dherrendoerfer/uCNC_controller/Extras/Rod-Robin/Z-Axis-Tool/Rod-Robin-Z-Tool_A.stl

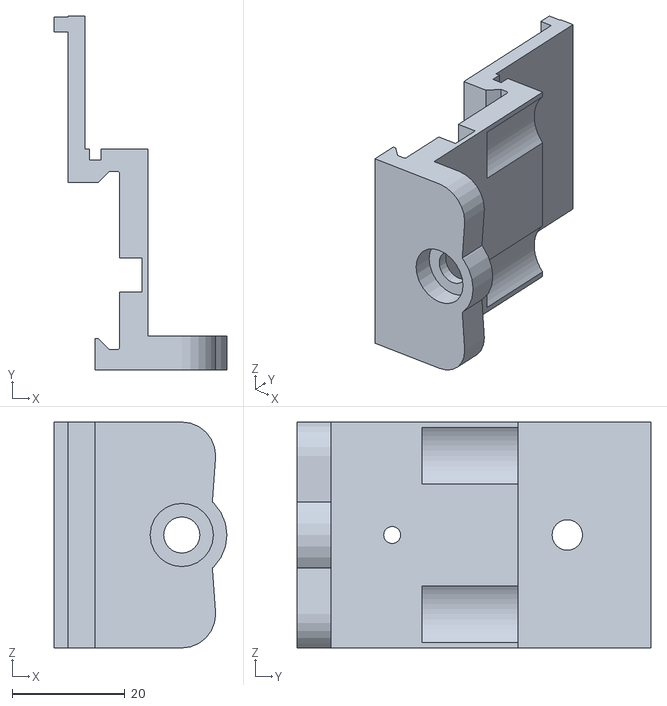
[picture p15: CAD file, 2017-02-15]
Extras/Rod-Robin/Z-Axis-Tool/Rod-Robin-Z-Tool_A.stl
30.6 x 62.6 x 40.0
