dherrendoerfer/uCNC_controller/Extras/Plotter_v4/Plotter_v4_Pillar_2.stl

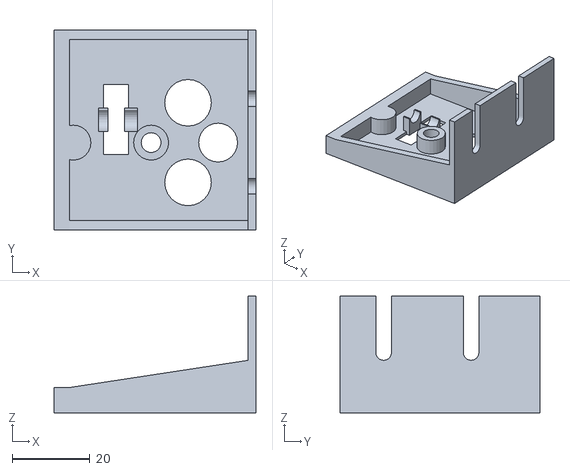
[picture p16: CAD file, 2018-01-10]
Extras/Plotter_v4/Plotter_v4_Pillar_2.stl
52.0 x 51.5 x 30.0
