dherrendoerfer/uCNC_controller/Extras/Rod-Robin/Rod-Robin-Pillar-B.stl

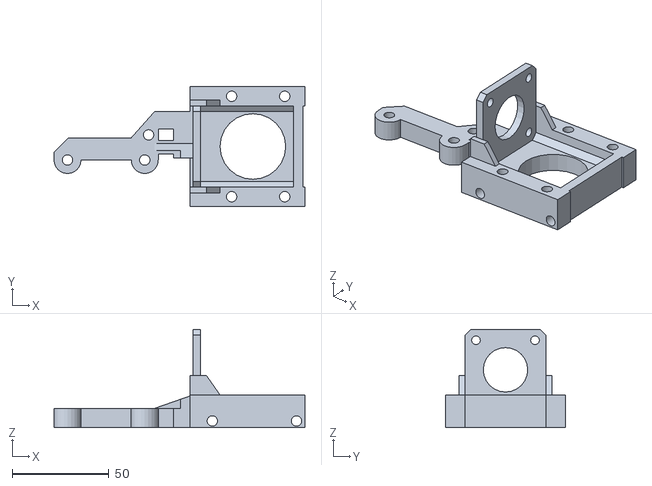
[picture p17: CAD file, 2017-02-15]
Extras/Rod-Robin/Rod-Robin-Pillar-B.stl
130.0 x 62.0 x 51.0
