dherrendoerfer/uCNC_controller/Extras/Rod-Robin/Z-Axis-Tool/Rod-Robin-Z-Tool_E.stl

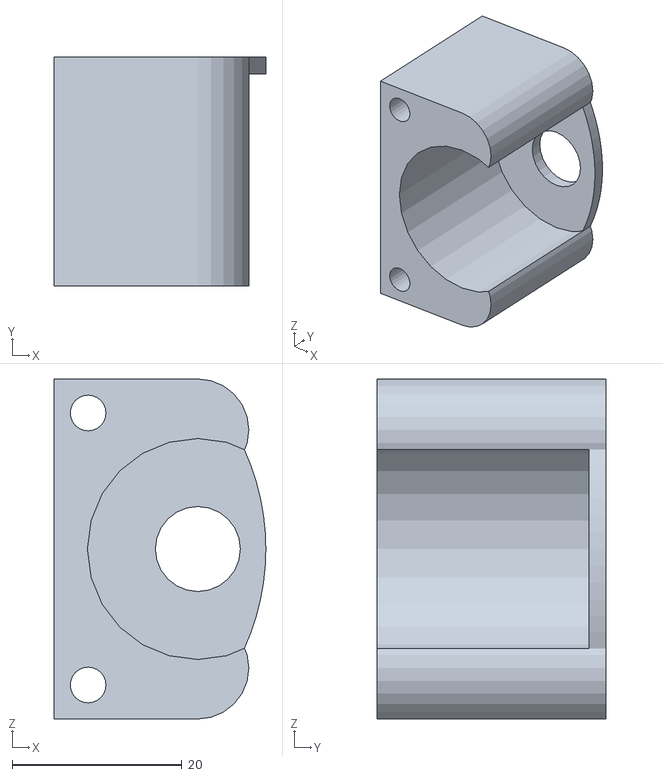
[picture p18: CAD file, 2017-02-15]
Extras/Rod-Robin/Z-Axis-Tool/Rod-Robin-Z-Tool_E.stl
24.9 x 27.0 x 40.0
