dherrendoerfer/uCNC_controller/Extras/Plotter_v4/Plotter_v4_Tool_Sled.stl

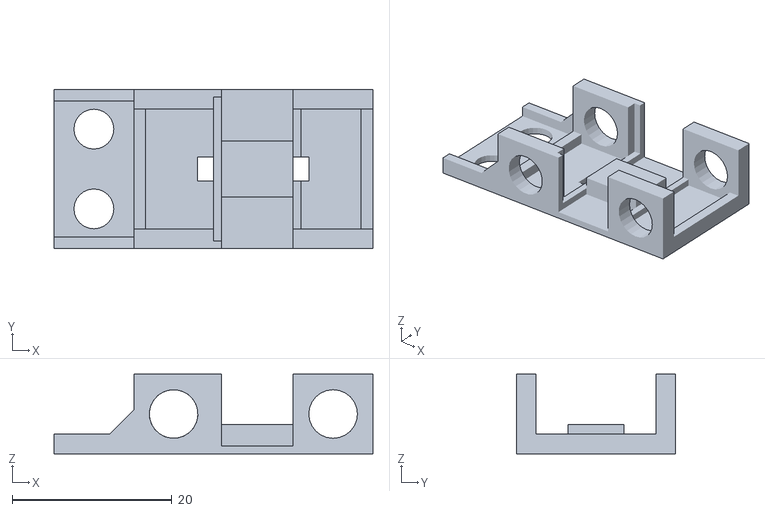
[picture p19: CAD file, 2018-01-10]
Extras/Plotter_v4/Plotter_v4_Tool_Sled.stl
40.0 x 20.0 x 10.0
