dherrendoerfer/uCNC_controller/Extras/Rod-Robin/Rod-Robin-H-Base-A.stl

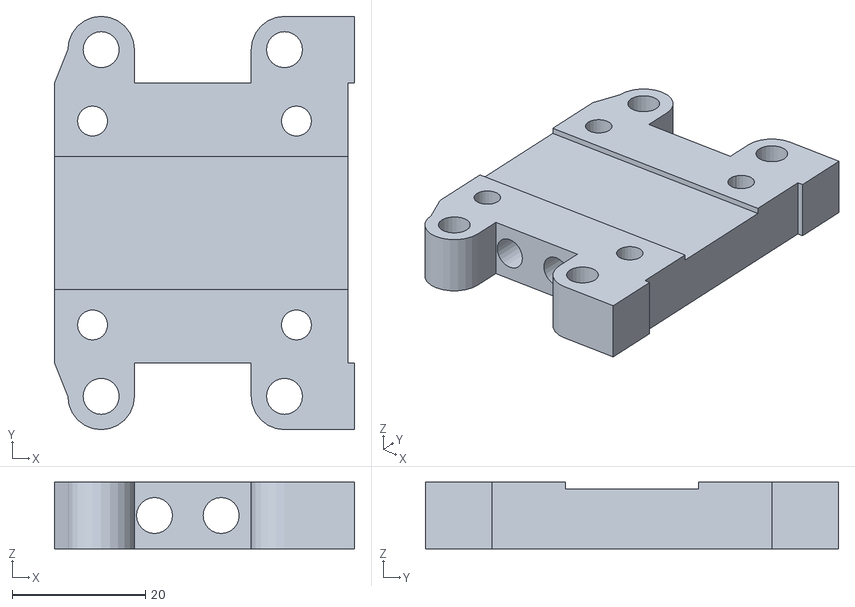
[picture p20: CAD file, 2017-02-15]
Extras/Rod-Robin/Rod-Robin-H-Base-A.stl
45.0 x 62.0 x 10.0
