dherrendoerfer/uCNC_controller/Extras/Rod-Robin/Z-Axis-Tool/Rod-Robin-Z-Tool_D.stl

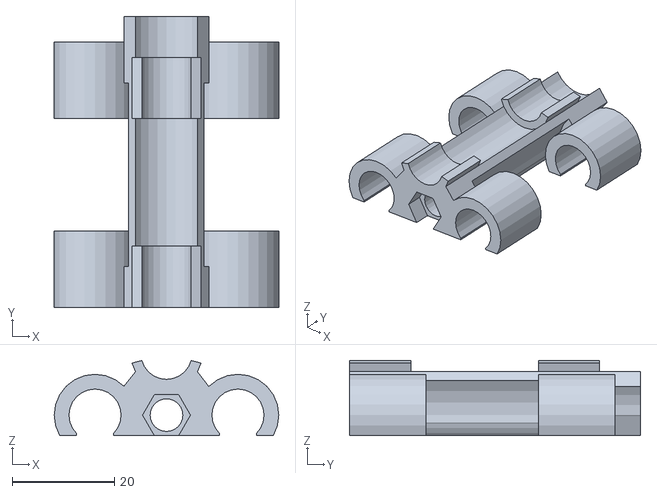
[picture p21: CAD file, 2017-02-15]
Extras/Rod-Robin/Z-Axis-Tool/Rod-Robin-Z-Tool_D.stl
44.0 x 57.0 x 14.7
