dherrendoerfer/uCNC_controller/Extras/Plotter_v4/Plotter_v4_AllParts.stl

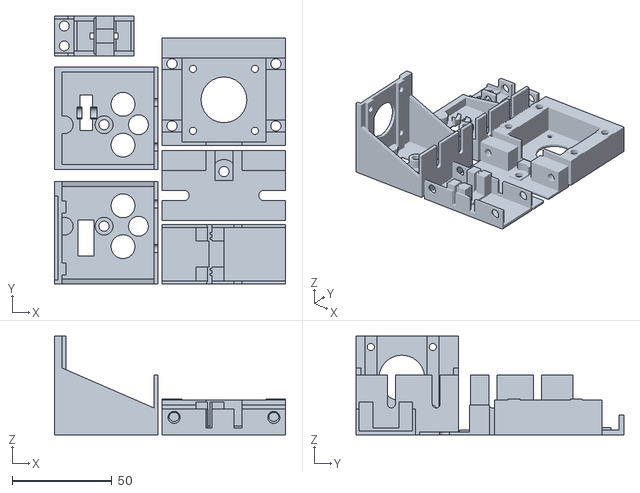
[picture p22: CAD file, 2016-12-31]
Extras/Plotter_v4/Plotter_v4_AllParts.stl
116.1 x 134.5 x 49.5
