dherrendoerfer/uCNC_controller/Extras/Rod-Robin/Rod-Robin-H-Base-C.stl

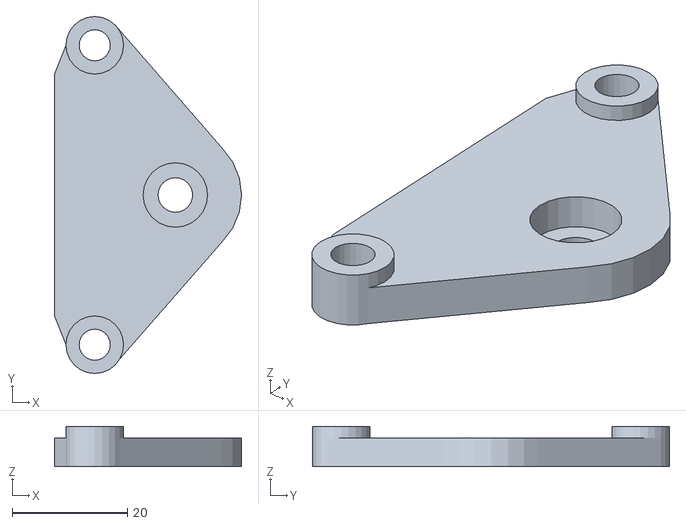
[picture p23: CAD file, 2017-02-15]
Extras/Rod-Robin/Rod-Robin-H-Base-C.stl
32.5 x 62.0 x 7.00
