dherrendoerfer/uCNC_controller/Extras/Rod-Robin/Rod-Robin-H-Base-B.stl

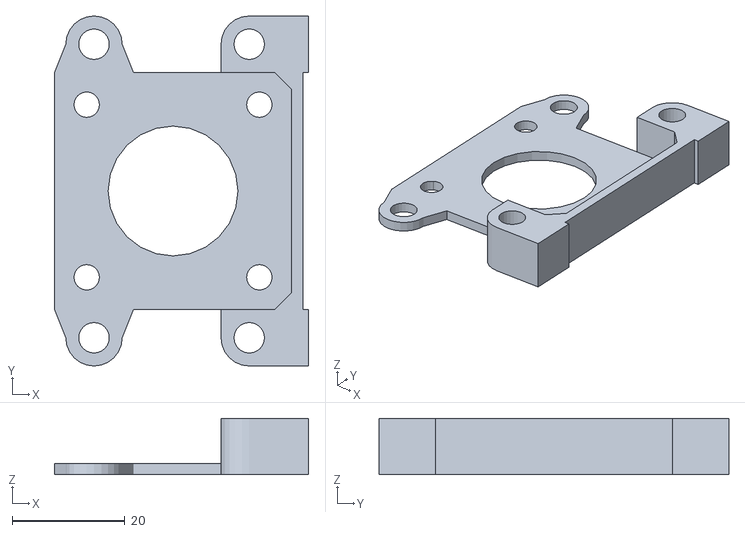
[picture p24: CAD file, 2017-02-15]
Extras/Rod-Robin/Rod-Robin-H-Base-B.stl
45.0 x 62.0 x 10.0
