dherrendoerfer/uCNC_controller/Extras/Rod-Robin/Rod-Robin-Table-A.stl

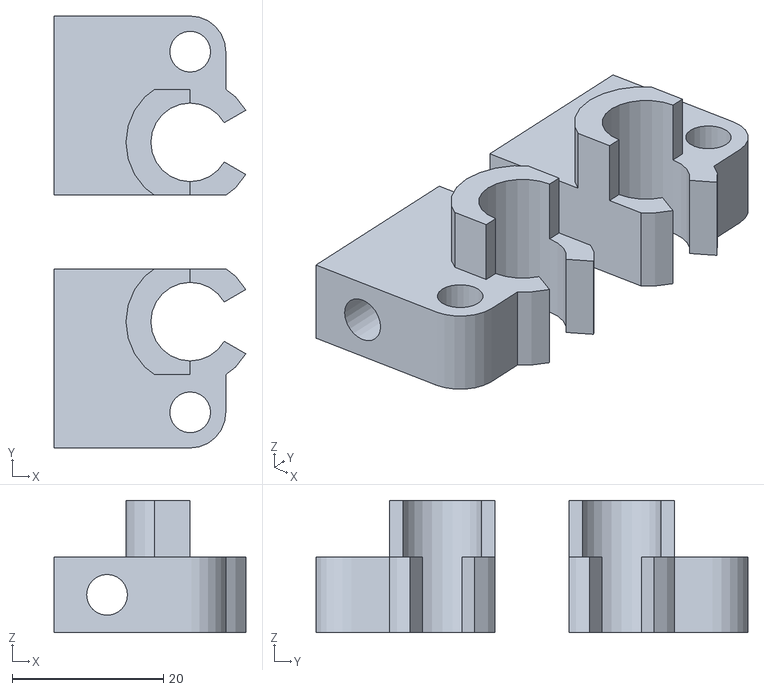
[picture p25: CAD file, 2017-02-15]
Extras/Rod-Robin/Rod-Robin-Table-A.stl
25.4 x 57.2 x 17.5
