dherrendoerfer/uCNC_controller/beta/uCNC_controller_v6/uCNC_move_planner.ino

/*
 * This file is part of uCNC_controller.
 *
 * Copyright (C) 2016,2017  D.Herrendoerfer
 *
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
 *   You should have received a copy of the GNU General Public License
 *   along with uCNC_controller.  If not, see <http://www.gnu.org/licenses/>.
 */

#define PLAN_MAX 7

struct planItem {
  unsigned int lineNo;
  posval_t targetX, targetY, targetZ;
  unsigned int feedHz;
  unsigned int feedStartHz;
} movePlan[8];

int currentPlanItem = 0;
int nextPlanItem = 0;

void plan_line(posval_t x2, posval_t y2, posval_t z2, float feedrate)
{
  posval_t n, deltax, deltay, deltaz, sgndeltax, sgndeltay, sgndeltaz, deltaxabs, deltayabs, deltazabs, x, y, z, maxdeltaabs;
  unsigned int feedHz; 
  unsigned int startHz; 

  deltax = x2 - X;
  deltay = y2 - Y;
  deltaz = z2 - Z;
  deltaxabs = abs(deltax);
  deltayabs = abs(deltay);
  deltazabs = abs(deltaz);
  sgndeltax = sgn(deltax);
  sgndeltay = sgn(deltay);
  sgndeltaz = sgn(deltaz);
  x = deltaxabs >> 1;
  y = deltayabs >> 1;
  z = deltazabs >> 1;

  // dX is biggest
  if(deltaxabs >= deltayabs && deltaxabs >= deltazabs){
    maxdeltaabs = deltaxabs;
    feedHz = feedrate * stepNumPerMillimeter_X;
    startHz = stepIssueStartFreq_X;
    
    if (stepIssueFrequency_X < feedHz)
      feedHz = stepIssueFrequency_X;    
  }
  // dY is biggest
  else if(deltayabs >= deltaxabs && deltayabs >= deltazabs){
    maxdeltaabs = deltayabs;
    feedHz = feedrate * stepNumPerMillimeter_Y;
    startHz = stepIssueStartFreq_Y;
    
    if (stepIssueFrequency_Y < feedHz)
      feedHz = stepIssueFrequency_Y;
  }
  // dZ is biggest
  else if(deltazabs >= deltaxabs && deltazabs >= deltayabs){
    maxdeltaabs = deltazabs;
    feedHz = feedrate * stepNumPerMillimeter_Z;
    startHz = stepIssueStartFreq_Z;

    if (stepIssueFrequency_Z < feedHz)
      feedHz = stepIssueFrequency_Z;
  }
  Serial.print("Feed rate:");
  Serial.print(feedHz);
  Serial.println("Hz");
  
  if (deltaxabs)  
    mStepperX.plan(0, sgndeltax, maxdeltaabs, deltaxabs, x, feedHz, startHz);

  if (deltayabs)  
    mStepperY.plan(0, sgndeltay, maxdeltaabs, deltayabs, y, feedHz, startHz);

  if (deltazabs)  
    mStepperZ.plan(0, sgndeltaz, maxdeltaabs, deltazabs, z, feedHz, startHz);

  X = x2;
  Y = y2;
  Z = z2;
}

void addPlanItem(unsigned int lineNo, posval_t x, posval_t y, posval_t z, unsigned int feedrateHz)
{
  movePlan[currentPlanItem].lineNo = lineNo;
  movePlan[currentPlanItem].targetX = x;
  movePlan[currentPlanItem].targetY = y;
  movePlan[currentPlanItem].targetZ = z;
  movePlan[currentPlanItem].feedHz = feedrateHz;
  
  if (++currentPlanItem == PLAN_MAX)
    currentPlanItem = 0;
}

void syncPlan()
{

}
