dherrendoerfer/uCNC_controller/uCNC_controller/uCNC_builtin.ino

/*
 * This file is part of uCNC_controller.
 *
 * Copyright (C) 2014  D.Herrendoerfer
 *
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
 *   You should have received a copy of the GNU General Public License
 *   along with uCNC_controller.  If not, see <http://www.gnu.org/licenses/>.
 */

/* Built-in functions for setup and debug purposes 
 * using these may require some tweaking           */

#ifdef BUILTIN
void calibratePattern()
{
  int i=0;

  /*Draw a line pattern in absolute step mode*/
  drawline(50,50,1000,50);
  drawline(1000,150,50,150);
  drawline(50,250,1000,250);
  drawline(1000,350,50,350);

  for (i=50; i<1000; i+=50)
    drawline(i,30,i,70);

  for (i=100; i<1000; i+=100)
    drawline(i,30,i,170);

  for (i=200; i<1000; i+=200)
    drawline(i,30,i,270);

  for (i=400; i<1000; i+=400)
    drawline(i,30,i,370);

  /*Draw a line pattern in 5,10,20,40mm spacing*/
  drawlinePos(5,25,60,25);
  drawlinePos(60,30,5,30);
  drawlinePos(5,35,60,35);
  drawlinePos(60,40,5,40);
  
  for (i=5; i<60; i+=5)
    drawlinePos(i,23,i,27);
  
  for (i=10; i<60; i+=10)
    drawlinePos(i,23,i,32);

  for (i=20; i<60; i+=20)
    drawlinePos(i,23,i,37);

  for (i=40; i<60; i+=40)
    drawlinePos(i,23,i,42);
}
#endif

#ifdef BUILTIN
void dumpSettings()
{
  Serial.print("Hello, this is uCNC_contoller version ");
  Serial.println(uCNC_Version,1);
  Serial.println("");
  Serial.println("current settings are:");
  Serial.println("");
  Serial.print("motorMode:");
  Serial.println(motorMode);
  Serial.println("Stepper positions:");
  Serial.print("X:");
  Serial.println(X);
  Serial.print("Y:");
  Serial.println(Y);
  Serial.print("Z:");
  Serial.println(Z);
  Serial.println("Absolute positions:");
  Serial.print("posX:");
  Serial.println(posX,3);
  Serial.print("posY:");
  Serial.println(posY,3);
  Serial.print("posZ:");
  Serial.println(posZ,3);
  Serial.println("Stepper settings:");
  Serial.print("stepsPerMillimeter_X:");
  Serial.println(stepsPerMillimeter_X, 3);
  Serial.print("stepsPerMillimeter_Y:");
  Serial.println(stepsPerMillimeter_Y, 3);
  Serial.print("stepsPerMillimeter_Z:");
  Serial.println(stepsPerMillimeter_Z, 3);
  Serial.println("Servo settings:");
  Serial.print("servoPosZfactor:");
  Serial.println(servoPosZfactor, 3);
  Serial.print("servoPosMax:");
  Serial.println(servoPosMax);
  Serial.print("servoPosMin:");
  Serial.println(servoPosMin);
  Serial.print("servoToolInc:");
  Serial.println(servoToolInc);
  Serial.print("EOM."); 
}
#endif
