dherrendoerfer/uCNC_controller/Extras/LED-HMD/led-hmd/led-hmd.ino

/*
 * This file is part of uCNC_controller.
 *
 * Copyright (C) 2017  D.Herrendoerfer
 *
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
 *   You should have received a copy of the GNU General Public License
 *   along with uCNC_controller.  If not, see <http://www.gnu.org/licenses/>.
 */

#include "FastLED.h"
 
#define DATA_PIN    6
#define LED_TYPE    WS2812B
#define COLOR_ORDER GRB
#define NUM_LEDS    506
#define BRIGHTNESS  25
 
CRGB leds[NUM_LEDS];

/* pix/Stormtrooper Pixel Head.png */
const PROGMEM unsigned char image0[]={231, 233, 232, 231, 233, 232, 231, 233, 232, 231, 233, 232, 231, 233, 232, 231, 233, 232, 231, 233, 232, 231, 233, 232, 231, 233, 232, 231, 233, 232, 231, 233, 232, 231, 233, 232, 231, 233, 232, 231, 233, 232, 231, 233, 232, 231, 233, 232, 231, 233, 232, 231, 233, 232, 231, 233, 232, 231, 233, 232, 231, 233, 232, 206, 210, 209, 206, 210, 209, 206, 210, 209, 206, 210, 209, 231, 233, 232, 231, 233, 232, 231, 233, 232, 231, 233, 232, 231, 233, 232, 231, 233, 232, 231, 233, 232, 231, 233, 232, 231, 233, 232, 206, 210, 209, 206, 210, 209, 206, 210, 209, 206, 210, 209, 206, 210, 209, 206, 210, 209, 206, 210, 209, 206, 210, 209, 231, 233, 232, 231, 233, 232, 231, 233, 232, 231, 233, 232, 231, 233, 232, 231, 233, 232, 231, 233, 232, 231, 233, 232, 206, 210, 209, 206, 210, 209, 206, 210, 209, 206, 210, 209, 206, 210, 209, 206, 210, 209, 206, 210, 209, 206, 210, 209, 206, 210, 209, 206, 210, 209, 231, 233, 232, 231, 233, 232, 231, 233, 232, 231, 233, 232, 0, 0, 0, 231, 233, 232, 231, 233, 232, 231, 233, 232, 231, 233, 232, 206, 210, 209, 206, 210, 209, 206, 210, 209, 206, 210, 209, 206, 210, 209, 206, 210, 209, 206, 210, 209, 206, 210, 209, 206, 210, 209, 206, 210, 209, 231, 233, 232, 231, 233, 232, 231, 233, 232, 231, 233, 232, 0, 0, 0, 0, 0, 0, 0, 0, 0, 231, 233, 232, 231, 233, 232, 231, 233, 232, 231, 233, 232, 206, 210, 209, 206, 210, 209, 206, 210, 209, 206, 210, 209, 206, 210, 209, 206, 210, 209, 206, 210, 209, 206, 210, 209, 206, 210, 209, 2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
0, 209, 206, 210, 209, 0, 0, 0, 0, 0, 0, 206, 210, 209, 206, 210, 209, 156, 158, 157, 0, 0, 0, 156, 158, 157, 156, 158, 157, 25, 25, 25, 46, 48, 47, 46, 48, 47, 25, 25, 25, 154, 156, 155, 154, 156, 155, 0, 0, 0, 154, 156, 155, 206, 210, 209, 206, 210, 209, 0, 0, 0, 206, 210, 209, 206, 210, 209, 0, 0, 0, 255, 255, 255, 0, 0, 0, 156, 158, 157, 46, 48, 47, 25, 25, 25, 25, 25, 25, 46, 48, 47, 154, 156, 155, 0, 0, 0, 255, 255, 255, 0, 0, 0, 206, 210, 209, 206, 210, 209, 206, 210, 209, 156, 158, 157, 0, 0, 0, 255, 255, 255, 46, 48, 47, 46, 48, 47, 25, 25, 25, 25, 25, 25, 46, 48, 47, 46, 48, 47, 154, 156, 155, 0, 0, 0, 154, 156, 155, 206, 210, 209, 206, 210, 209, 206, 210, 209, 206, 210, 209, 0, 0, 0, 0, 0, 0, 0, 0, 0, 0, 0, 0, 206, 210, 209, 206, 210, 209, 206, 210, 209, 0, 0, 0, 0, 0, 0, 0, 0, 0, 0, 0, 0, 0, 0, 0, 0, 0, 0, };

/* flaming eye */
const PROGMEM unsigned char image1[]={0, 0, 0, 0, 0, 0, 0, 0, 0, 0, 0, 0, 0, 0, 0, 0, 0, 0, 0, 0, 0, 0, 0, 0, 0, 0, 0, 0, 0, 0, 0, 0, 0, 0, 0, 0, 0, 0, 0, 0, 0, 0, 0, 0, 0, 0, 0, 0, 0, 0, 0, 0, 0, 0, 0, 0, 0, 0, 0, 0, 0, 0, 0, 0, 0, 0, 0, 0, 0, 0, 0, 0, 0, 0, 0, 0, 0, 0, 0, 0, 0, 0, 0, 0, 0, 0, 0, 0, 0, 0, 0, 0, 0, 0, 0, 0, 0, 0, 0, 0, 0, 0, 0, 0, 0, 0, 0, 0, 0, 0, 0, 0, 0, 0, 0, 0, 0, 0, 0, 0, 0, 0, 0, 0, 0, 0, 0, 0, 0, 0, 0, 0, 0, 0, 0, 0, 0, 0, 0, 0, 0, 0, 0, 0, 0, 0, 0, 0, 0, 0, 0, 0, 0, 0, 0, 0, 0, 0, 0, 0, 0, 0, 0, 0, 0, 0, 0, 0, 0, 0, 0, 0, 0, 0, 0, 0, 0, 0, 0, 0, 0, 0, 0, 0, 0, 0, 0, 0, 0, 255, 17, 0, 0, 0, 0, 0, 0, 0, 0, 0, 0, 0, 0, 0, 0, 0, 0, 0, 0, 0, 0, 0, 0, 0, 0, 0, 0, 0, 0, 0, 0, 0, 0, 0, 0, 0, 0, 0, 0, 0, 0, 0, 0, 0, 0, 0, 0, 255, 17, 0, 0, 0, 0, 0, 0, 0, 0, 0, 0, 0, 0, 0, 0, 0, 0, 0, 0, 0, 0, 0, 0, 0, 0, 0, 0, 0, 0, 0, 0, 0, 0, 0, 0, 0, 0, 0, 0, 0, 0, 0, 0, 0, 0, 0, 0, 0, 0, 0, 0, 0, 0, 0, 0, 0, 0, 0, 0, 0, 0, 0, 0, 0, 0, 0, 0, 0, 0, 0, 0, 0, 0, 0, 255, 17, 0, 0, 0, 0, 0, 0, 0, 0, 0, 0, 0, 0, 0, 0, 0, 0, 0, 0, 0, 0, 0, 0, 0, 0, 0, 0, 0, 0, 0, 0, 0, 0, 0, 0, 0, 0, 0, 0, 0, 0, 0, 0, 0, 0, 0, 0, 0, 0, 0, 0, 0, 0, 0, 0, 0, 219, 15, 0, 219, 15, 0, 0, 0, 0, 0, 0, 0, 0, 0, 0, 0, 0, 0, 0, 0, 0, 0, 0, 0, 0, 0, 0, 0, 0, 0, 0, 0, 0, 0, 0, 0, 255, 255, 255, 255, 255, 255, 255, 255, 255, 255, 255, 255, 255, 255, 255, 255, 255, 255, 255, 255, 255, 255, 255, 255, 0, 0, 0, 0, 0, 0, 219, 15, 0, 219, 15, 0, 0, 0, 0, 0, 0, 0, 0, 0, 0, 255, 17, 0, 0, 0, 0, 0, 0, 0, 0, 0, 0, 0, 0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

/* pix/smiley-1635449_960_720.png */
const PROGMEM unsigned char image2[]={0, 0, 0, 0, 0, 0, 0, 0, 0, 0, 0, 0, 0, 0, 0, 0, 0, 0, 0, 0, 0, 0, 0, 0, 25, 25, 0, 58, 57, 0, 79, 76, 0, 79, 76, 0, 58, 57, 0, 25, 25, 0, 0, 0, 0, 0, 0, 0, 0, 0, 0, 9, 8, 0, 0, 0, 0, 0, 0, 0, 0, 0, 0, 0, 0, 0, 255, 255, 0, 255, 255, 0, 0, 0, 0, 0, 0, 0, 0, 0, 0, 0, 0, 0, 9, 8, 0, 0, 0, 0, 0, 0, 0, 0, 0, 0, 0, 0, 0, 255, 255, 0, 255, 251, 0, 255, 244, 0, 254, 240, 0, 252, 239, 0, 252, 239, 0, 254, 240, 0, 255, 244, 0, 255, 251, 0, 255, 255, 0, 0, 0, 0, 0, 0, 0, 0, 0, 0, 0, 0, 0, 0, 0, 0, 0, 0, 0, 255, 248, 0, 255, 245, 0, 255, 252, 0, 254, 241, 0, 255, 241, 0, 255, 242, 0, 255, 242, 0, 255, 241, 0, 254, 241, 0, 255, 252, 0, 255, 245, 0, 255, 248, 0, 0, 0, 0, 0, 0, 0, 0, 0, 0, 0, 0, 0, 0, 0, 0, 255, 255, 0, 251, 238, 0, 255, 248, 0, 0, 0, 0, 0, 0, 0, 255, 245, 0, 254, 244, 0, 254, 241, 0, 254, 242, 0, 254, 243, 0, 255, 246, 0, 0, 0, 0, 0, 0, 0, 255, 248, 0, 251, 238, 0, 255, 255, 0, 0, 0, 0, 0, 0, 0, 0, 0, 0, 0, 0, 0, 0, 0, 0, 249, 238, 0, 253, 248, 0, 0, 0, 0, 16, 15, 0, 0, 0, 0, 0, 0, 0, 255, 252, 0, 253, 240, 0, 253, 239, 0, 255, 252, 0, 0, 0, 0, 0, 0, 0, 14, 14, 0, 0, 0, 0, 253, 249, 0, 248, 238, 0, 0, 0, 0, 0, 0, 0, 0, 0, 0, 0, 0, 0, 0, 0, 0, 254, 250, 0, 249, 236, 0, 255, 255, 0, 0, 0, 0, 0, 0, 0, 5, 5, 0, 0, 0, 0, 0, 0, 0, 255, 249, 0, 255, 248, 0, 215, 204, 0, 0, 0, 0, 5, 5, 0, 0, 0, 0, 0, 0, 0, 255, 255, 0, 249, 236, 0, 254, 250, 0, 0, 0, 0, 0, 0, 0, 0, 0, 0, 0, 0, 0, 255, 255, 0, 251, 237, 0, 255, 243, 0, 252, 240, 0, 0, 0, 0, 1, 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

/* pix/new/smiley-1635449_960_720 Kopie.png */
const PROGMEM unsigned char image3[]={0, 0, 0, 0, 0, 0, 0, 0, 0, 0, 0, 0, 0, 0, 0, 0, 0, 0, 0, 0, 0, 0, 0, 0, 255, 242, 0, 255, 242, 0, 255, 242, 0, 255, 242, 0, 255, 242, 0, 255, 242, 0, 0, 0, 0, 0, 0, 0, 0, 0, 0, 255, 242, 0, 255, 242, 0, 255, 242, 0, 255, 242, 0, 255, 242, 0, 255, 242, 0, 255, 242, 0, 255, 242, 0, 255, 242, 0, 255, 242, 0, 255, 242, 0, 255, 242, 0, 0, 0, 0, 255, 242, 0, 255, 242, 0, 255, 242, 0, 255, 242, 0, 255, 242, 0, 255, 242, 0, 255, 242, 0, 255, 242, 0, 255, 242, 0, 255, 242, 0, 255, 242, 0, 255, 242, 0, 255, 242, 0, 255, 242, 0, 255, 242, 0, 255, 242, 0, 255, 242, 0, 255, 242, 0, 255, 242, 0, 255, 242, 0, 255, 242, 0, 255, 242, 0, 255, 242, 0, 255, 242, 0, 255, 242, 0, 255, 242, 0, 255, 242, 0, 255, 242, 0, 255, 242, 0, 255, 242, 0, 255, 242, 0, 255, 242, 0, 255, 242, 0, 255, 242, 0, 255, 242, 0, 255, 242, 0, 255, 242, 0, 255, 242, 0, 255, 242, 0, 255, 242, 0, 255, 242, 0, 255, 242, 0, 255, 242, 0, 255, 242, 0, 255, 242, 0, 255, 242, 0, 255, 242, 0, 255, 242, 0, 255, 242, 0, 255, 242, 0, 255, 242, 0, 255, 242, 0, 255, 242, 0, 255, 242, 0, 0, 0, 0, 255, 242, 0, 255, 242, 0, 255, 242, 0, 255, 242, 0, 255, 242, 0, 255, 242, 0, 255, 242, 0, 255, 242, 0, 255, 242, 0, 255, 242, 0, 255, 242, 0, 255, 242, 0, 255, 242, 0, 255, 242, 0, 255, 242, 0, 255, 242, 0, 255, 242, 0, 255, 242, 0, 255, 242, 0, 255, 242, 0, 0, 0, 0, 255, 242, 0, 255, 242, 0, 255, 242, 0, 255, 242, 0, 255, 242, 0, 0, 0, 0, 0, 0, 0, 0, 0, 0, 255, 242, 0, 255, 242, 0, 255, 242, 0, 255, 242,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
255, 242, 0, 0, 0, 0, 0, 0, 0, 4, 4, 0, 255, 242, 0, 255, 242, 0, 255, 242, 0, 255, 242, 0, 255, 242, 0, 255, 242, 0, 0, 0, 0, 0, 0, 0, 0, 0, 0, 0, 0, 0, 0, 0, 0, 0, 0, 0, 0, 0, 0, 0, 0, 0, };
/* pix/new/smiley-1635449_960_720.png */
const PROGMEM unsigned char image3b[]={0, 0, 0, 0, 0, 0, 0, 0, 0, 0, 0, 0, 0, 0, 0, 0, 0, 0, 0, 0, 0, 0, 0, 0, 255, 242, 0, 255, 242, 0, 255, 242, 0, 255, 242, 0, 255, 242, 0, 255, 242, 0, 0, 0, 0, 0, 0, 0, 0, 0, 0, 255, 242, 0, 255, 242, 0, 255, 242, 0, 255, 242, 0, 255, 242, 0, 255, 242, 0, 255, 242, 0, 255, 242, 0, 255, 242, 0, 255, 242, 0, 255, 242, 0, 255, 242, 0, 0, 0, 0, 255, 242, 0, 255, 242, 0, 255, 242, 0, 255, 242, 0, 255, 242, 0, 255, 242, 0, 255, 242, 0, 255, 242, 0, 255, 242, 0, 255, 242, 0, 255, 242, 0, 255, 242, 0, 255, 242, 0, 255, 242, 0, 255, 242, 0, 255, 242, 0, 255, 242, 0, 255, 242, 0, 255, 242, 0, 255, 242, 0, 255, 242, 0, 255, 242, 0, 255, 242, 0, 255, 242, 0, 255, 242, 0, 255, 242, 0, 255, 242, 0, 255, 242, 0, 255, 242, 0, 255, 242, 0, 255, 242, 0, 255, 242, 0, 255, 242, 0, 255, 242, 0, 255, 242, 0, 255, 242, 0, 255, 242, 0, 255, 242, 0, 255, 242, 0, 255, 242, 0, 255, 242, 0, 255, 242, 0, 255, 242, 0, 255, 242, 0, 255, 242, 0, 255, 242, 0, 255, 242, 0, 255, 242, 0, 255, 242, 0, 255, 242, 0, 255, 242, 0, 255, 242, 0, 255, 242, 0, 255, 242, 0, 0, 0, 0, 255, 242, 0, 255, 242, 0, 255, 242, 0, 255, 242, 0, 255, 242, 0, 255, 242, 0, 255, 242, 0, 255, 242, 0, 255, 242, 0, 255, 242, 0, 255, 242, 0, 255, 242, 0, 255, 242, 0, 255, 242, 0, 255, 242, 0, 255, 242, 0, 255, 242, 0, 255, 242, 0, 255, 242, 0, 255, 242, 0, 0, 0, 0, 255, 242, 0, 255, 242, 0, 255, 242, 0, 255, 242, 0, 255, 242, 0, 255, 242, 0, 255, 242, 0, 255, 242, 0, 255, 242, 0, 255, 242, 0, 255, 242,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
, 242, 0, 255, 242, 0, 255, 242, 0, 255, 242, 0, 255, 242, 0, 0, 0, 0, 0, 0, 0, 4, 4, 0, 255, 242, 0, 255, 242, 0, 255, 242, 0, 255, 242, 0, 255, 242, 0, 255, 242, 0, 0, 0, 0, 0, 0, 0, 0, 0, 0, 0, 0, 0, 0, 0, 0, 0, 0, 0, 0, 0, 0, 0, 0, 0, };


/* pix/new/Jack-skellington.jpg */
const PROGMEM unsigned char image4[]={0, 1, 0, 2, 4, 1, 0, 2, 0, 0, 1, 0, 0, 2, 0, 0, 2, 0, 2, 4, 1, 0, 1, 0, 145, 147, 144, 174, 176, 173, 182, 187, 183, 179, 184, 180, 171, 177, 173, 139, 145, 141, 4, 4, 4, 0, 0, 0, 0, 1, 0, 0, 1, 0, 211, 213, 210, 242, 244, 241, 252, 255, 253, 252, 255, 253, 250, 255, 252, 235, 244, 239, 218, 227, 222, 212, 221, 216, 201, 205, 206, 189, 193, 192, 161, 163, 162, 2, 4, 3, 3, 8, 4, 180, 185, 181, 248, 253, 249, 249, 251, 250, 252, 255, 255, 244, 248, 247, 251, 255, 255, 234, 243, 240, 211, 220, 217, 193, 204, 200, 178, 189, 185, 187, 193, 193, 197, 203, 203, 205, 209, 210, 197, 199, 198, 4, 4, 4, 0, 1, 0, 203, 207, 206, 243, 249, 245, 225, 231, 227, 237, 241, 240, 243, 247, 246, 244, 250, 248, 219, 225, 223, 208, 217, 214, 188, 199, 195, 169, 180, 176, 166, 177, 173, 175, 184, 183, 203, 209, 209, 173, 174, 176, 172, 172, 174, 193, 191, 192, 1, 0, 0, 0, 3, 2, 209, 213, 214, 243, 249, 249, 221, 230, 229, 221, 230, 229, 209, 215, 213, 224, 230, 228, 220, 226, 224, 215, 221, 219, 192, 198, 196, 178, 187, 184, 168, 177, 174, 159, 168, 165, 194, 199, 202, 128, 132, 133, 79, 79, 81, 62, 60, 63, 108, 104, 105, 184, 182, 183, 0, 0, 0, 0, 1, 0, 188, 192, 193, 204, 209, 212, 114, 122, 124, 116, 124, 127, 161, 171, 173, 212, 218, 216, 206, 212, 210, 200, 206, 204, 197, 203, 201, 194, 200, 198, 179, 185, 183, 179, 183, 182, 201, 205, 204, 149, 150, 154, 52, 51, 56, 44, 39, 43, 4, 0, 2, 23, 17, 19, 145, 141, 142, 196, 196, 194, 0, 1, 0, 253, 255, 254, 206,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
 128, 128, 7, 0, 0, 0, 0, 2, 0, 0, 4, 125, 126, 130, 124, 128, 131, 140, 145, 148, 133, 138, 142, 144, 149, 153, 158, 161, 166, 149, 150, 154, 157, 155, 158, 147, 143, 144, 142, 133, 134, 141, 132, 133, 130, 122, 120, 98, 90, 88, 4, 0, 0, 0, 0, 4, 0, 0, 4, 0, 4, 7, 74, 82, 85, 111, 118, 124, 132, 137, 143, 146, 149, 156, 153, 154, 159, 135, 133, 136, 123, 118, 122, 102, 93, 94, 4, 0, 0, 3, 0, 0, 1, 0, 0, 0, 0, 0, 0, 0, 0, 0, 0, 0, 0, 0, 0, 0, 0, 0, 0, 0, 0, 0, 0, 0, 0, 0, 0, 0, 0, 0, 0, 0, 0, 0, 0, 0, 0, 0, 0, 0, 0, 0, 0, 0, 0, 0, 0, 0, 0, 0, 0, };
/* pix/new/Jack-skellington Kopie.jpg */
const PROGMEM unsigned char image4b[]={0, 1, 0, 3, 5, 2, 0, 1, 0, 0, 1, 0, 0, 3, 0, 0, 2, 0, 4, 6, 3, 0, 1, 0, 148, 150, 147, 173, 175, 172, 180, 185, 181, 180, 185, 181, 174, 180, 176, 140, 146, 142, 4, 4, 4, 0, 0, 0, 0, 1, 0, 0, 1, 0, 211, 213, 210, 243, 245, 242, 252, 255, 253, 252, 255, 253, 247, 253, 249, 235, 244, 239, 220, 229, 224, 211, 220, 215, 200, 204, 205, 188, 192, 191, 160, 162, 161, 3, 5, 4, 4, 9, 5, 181, 186, 182, 249, 254, 250, 247, 249, 248, 252, 255, 255, 241, 245, 244, 251, 255, 255, 231, 240, 237, 210, 219, 216, 193, 204, 200, 176, 187, 183, 188, 194, 194, 197, 203, 203, 205, 209, 210, 198, 200, 199, 6, 6, 6, 0, 1, 0, 204, 208, 207, 243, 249, 245, 225, 231, 227, 237, 241, 240, 243, 247, 246, 244, 250, 248, 218, 224, 222, 209, 218, 215, 190, 201, 197, 170, 181, 177, 164, 175, 171, 177, 186, 185, 203, 209, 209, 172, 173, 175, 171, 171, 173, 194, 192, 193, 1, 0, 0, 0, 4, 3, 209, 213, 214, 242, 248, 248, 221, 230, 229, 220, 229, 228, 209, 215, 213, 225, 231, 229, 220, 226, 224, 216, 222, 220, 193, 199, 197, 178, 187, 184, 168, 177, 174, 158, 167, 164, 194, 199, 202, 128, 132, 133, 79, 79, 81, 61, 59, 62, 107, 103, 104, 184, 182, 183, 1, 1, 0, 0, 2, 1, 188, 192, 193, 204, 209, 212, 113, 121, 123, 116, 124, 127, 161, 171, 173, 211, 217, 215, 205, 211, 209, 200, 206, 204, 197, 203, 201, 193, 199, 197, 178, 184, 182, 178, 182, 181, 201, 205, 204, 148, 149, 153, 53, 52, 57, 45, 40, 44, 4, 0, 2, 23, 17, 19, 145, 141, 142, 198, 198, 196, 0, 1, 0, 253, 255, 254, 206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
 130, 133, 126, 121, 125, 105, 96, 97, 5, 0, 0, 1, 0, 0, 3, 3, 3, 0, 0, 0, 0, 0, 0, 0, 0, 0, 0, 0, 0, 0, 0, 0, 0, 0, 0, 0, 0, 0, 0, 0, 0, 0, 0, 0, 0, 0, 0, 0, 0, 0, 0, 0, 0, 0, 0, 0, 0, 0, 0, 0, 0, 0, 0, 0, 0, };


/* pix/Sally.jpg */
const PROGMEM unsigned char image5[]={2, 2, 2, 1, 1, 1, 1, 0, 0, 2, 2, 1, 3, 3, 3, 3, 3, 3, 0, 0, 0, 0, 0, 0, 0, 0, 0, 0, 1, 2, 1, 4, 4, 0, 0, 0, 0, 0, 0, 0, 0, 0, 0, 0, 0, 2, 2, 2, 0, 0, 0, 0, 0, 0, 40, 42, 38, 76, 89, 86, 98, 118, 113, 119, 139, 132, 115, 138, 131, 110, 123, 115, 99, 105, 97, 73, 79, 72, 32, 34, 32, 0, 0, 0, 0, 0, 0, 3, 3, 3, 0, 0, 0, 20, 20, 18, 119, 128, 119, 143, 174, 167, 157, 190, 184, 177, 194, 185, 173, 183, 171, 170, 180, 168, 169, 179, 168, 166, 176, 165, 162, 172, 159, 149, 158, 145, 107, 113, 103, 29, 30, 28, 0, 0, 0, 3, 3, 3, 0, 0, 0, 31, 33, 30, 160, 171, 160, 134, 179, 179, 135, 182, 192, 156, 191, 199, 156, 186, 187, 180, 192, 183, 178, 188, 179, 178, 188, 179, 176, 188, 179, 157, 179, 175, 143, 174, 175, 152, 177, 173, 152, 164, 153, 63, 67, 60, 0, 0, 0, 3, 3, 3, 0, 0, 0, 25, 26, 24, 166, 179, 170, 143, 189, 193, 127, 186, 201, 155, 197, 211, 156, 195, 205, 170, 209, 216, 175, 198, 196, 193, 202, 193, 188, 198, 190, 171, 193, 192, 149, 190, 202, 143, 190, 204, 145, 192, 207, 148, 185, 192, 161, 178, 167, 63, 67, 59, 0, 0, 0, 3, 3, 3, 2, 2, 2, 6, 6, 6, 148, 158, 148, 177, 206, 206, 142, 194, 206, 100, 132, 140, 35, 46, 48, 22, 28, 28, 125, 152, 157, 178, 211, 216, 195, 206, 197, 191, 203, 195, 156, 192, 200, 90, 122, 129, 57, 76, 78, 77, 102, 109, 122, 161, 174, 151, 193, 202, 159, 173, 163, 34, 35, 31, 0, 0, 0, 3, 3, 3, 0, 0, 0, 81, 86, 81, 200, 218, 212, 169, 204, 209, 78, 96, 100, 0, 0, 0, 0, 0, 0, 0, 0, 0, 36, 47, 48, 173, 209, 216, 192, 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
, 2, 2, 2, 2, 2, 2, 0, 0, 0, 8, 9, 8, 31, 34, 30, 42, 44, 39, 53, 54, 48, 46, 46, 42, 42, 43, 40, 32, 35, 32, 5, 5, 5, 0, 0, 0, 3, 3, 3, 1, 1, 1, 3, 3, 3, 0, 0, 0, 0, 0, 0, 0, 0, 0, 0, 0, 0, 0, 0, 0, 0, 0, 0, 0, 0, 0, 0, 0, 0, 2, 2, 2, 3, 3, 3, 3, 3, 3, 3, 3, 3, 3, 3, 3, 3, 3, 3, 3, 3, 2, };
/* pix/new/scary.png */
const PROGMEM unsigned char image6[]={212, 212, 212, 232, 232, 232, 230, 230, 230, 230, 230, 230, 230, 230, 230, 235, 235, 235, 0, 0, 0, 204, 204, 204, 232, 232, 232, 230, 230, 230, 230, 230, 230, 230, 230, 230, 230, 230, 230, 230, 230, 230, 230, 230, 230, 0, 0, 0, 0, 0, 0, 0, 0, 0, 204, 204, 204, 204, 204, 204, 230, 230, 230, 230, 230, 230, 230, 230, 230, 230, 230, 230, 230, 230, 230, 230, 230, 230, 230, 230, 230, 230, 230, 230, 0, 0, 0, 0, 0, 0, 0, 0, 0, 0, 0, 0, 204, 204, 204, 204, 204, 204, 230, 230, 230, 230, 230, 230, 230, 230, 230, 230, 230, 230, 230, 230, 230, 230, 230, 230, 230, 230, 230, 230, 230, 230, 230, 230, 230, 230, 230, 230, 0, 0, 0, 0, 0, 0, 0, 0, 0, 0, 0, 0, 0, 0, 0, 204, 204, 204, 204, 204, 204, 230, 230, 230, 230, 230, 230, 230, 230, 230, 230, 230, 230, 230, 230, 230, 230, 230, 230, 230, 230, 230, 230, 230, 230, 230, 230, 230, 230, 230, 230, 0, 0, 0, 0, 0, 0, 0, 0, 0, 0, 0, 0, 0, 0, 0, 0, 0, 0, 204, 204, 204, 204, 204, 204, 204, 204, 204, 230, 230, 230, 230, 230, 230, 230, 230, 230, 230, 230, 230, 230, 230, 230, 230, 230, 230, 230, 230, 230, 230, 230, 230, 230, 230, 230, 230, 230, 230, 230, 230, 230, 0, 0, 0, 0, 0, 0, 0, 0, 0, 0, 0, 0, 0, 0, 0, 0, 0, 0, 0, 0, 0, 204, 204, 204, 204, 204, 204, 204, 204, 204, 230, 230, 230, 230, 230, 230, 230, 230, 230, 204, 204, 204, 204, 204, 204, 230, 230, 230, 230, 230, 230, 230, 230, 230, 230, 230, 230, 230, 230, 230, 230, 230, 230, 0, 0, 0, 0, 0, 0, 0, 0, 0, 0, 0, 0, 0, 0, 0, 0, 0, 0, 0, 0, 0, 0, 0, 0, 204, 204, 204, 2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
30, 230, 230, 228, 228, 228, 0, 0, 0, };
/* pix/new/Pumpkin Pixel Head.png */
const PROGMEM unsigned char image7[]={0, 0, 0, 0, 0, 0, 0, 0, 0, 0, 0, 0, 0, 0, 0, 0, 0, 0, 0, 0, 0, 0, 0, 0, 0, 0, 0, 0, 0, 0, 0, 0, 0, 0, 0, 0, 0, 0, 0, 0, 0, 0, 0, 0, 0, 0, 0, 0, 0, 0, 0, 0, 0, 0, 0, 0, 0, 0, 0, 0, 0, 0, 0, 0, 0, 0, 0, 0, 0, 0, 0, 0, 0, 0, 0, 0, 0, 0, 0, 0, 0, 0, 0, 0, 0, 0, 0, 0, 0, 0, 0, 0, 0, 0, 0, 0, 0, 0, 0, 0, 0, 0, 0, 0, 0, 0, 0, 0, 0, 0, 0, 0, 0, 0, 0, 0, 0, 0, 0, 0, 0, 0, 0, 0, 0, 0, 0, 0, 0, 0, 0, 0, 0, 0, 0, 0, 0, 0, 0, 0, 0, 0, 0, 0, 0, 0, 0, 0, 0, 0, 0, 0, 0, 0, 0, 0, 0, 0, 0, 0, 0, 0, 0, 0, 0, 0, 0, 0, 0, 0, 0, 0, 0, 0, 0, 0, 0, 0, 0, 0, 0, 0, 0, 0, 0, 0, 0, 0, 0, 0, 0, 0, 0, 0, 0, 0, 0, 0, 0, 0, 0, 0, 0, 0, 0, 0, 0, 0, 0, 0, 0, 0, 0, 0, 0, 0, 0, 0, 0, 0, 0, 0, 0, 0, 0, 0, 0, 0, 0, 0, 0, 0, 0, 0, 0, 0, 0, 0, 0, 0, 0, 0, 0, 0, 0, 0, 0, 0, 0, 0, 0, 0, 0, 0, 0, 0, 0, 0, 0, 0, 0, 0, 0, 0, 0, 0, 0, 0, 0, 0, 0, 0, 0, 0, 0, 0, 0, 0, 0, 0, 0, 0, 0, 0, 0, 0, 0, 0, 0, 0, 0, 0, 0, 0, 0, 0, 0, 0, 0, 0, 0, 0, 0, 0, 0, 0, 0, 0, 0, 0, 0, 0, 0, 0, 0, 0, 0, 0, 0, 0, 0, 0, 0, 0, 0, 0, 0, 0, 0, 0, 0, 0, 0, 0, 0, 0, 0, 0, 0, 0, 0, 0, 0, 0, 0, 0, 0, 0, 0, 0, 0, 153, 154, 54, 0, 0, 0, 0, 0, 0, 0, 0, 0, 0, 0, 0, 0, 0, 0, 0, 0, 0, 0, 0, 0, 0, 0, 0, 0, 0, 0, 0, 0, 0, 0, 0, 0, 0, 0, 0, 0, 0, 0, 0, 0, 0, 0, 0, 0, 0, 0, 0, 0, 0, 0, 0, 0, 0, 255, 214, 111, 255, 184, 79, 255, 214, 111, 0, 0, 0, 153, 154, 54, 0, 0, 0, 255, 214, 111, 255, 184, 79, 255, 214, 111, 0, 0, 0, 0, 0, 0, 0, 0, 0, 0, 0, 0, 0, 0, 0, 0, 0, 0, 0, 0, 0, 0, 0, 0, 0, 0, 0, 0, 0, 0, 0, 0, 0, 0, 0, 0, 0, 0,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



void setup() {
  delay(30); // initial delay of a few seconds is recommended
  FastLED.addLeds<WS2812, DATA_PIN, GRB>(leds, NUM_LEDS);
  FastLED.setBrightness(BRIGHTNESS);// global brightness
  
  /* Switches for the remote control */
  pinMode( 2,INPUT_PULLUP);
  pinMode( 3,INPUT_PULLUP);
}
 

// main program
void loop() {
  int i,a,b,x;
  char red,green,blue;
  b=0;
  a=0;
  
  while ( true ) {
    /* Display an image */
    x=0;
    for ( i=0 ; i < NUM_LEDS ; i++) {
      red = pgm_read_byte(&(images[a+b][x++]));
      green = pgm_read_byte(&(images[a+b][x++]));
      blue = pgm_read_byte(&(images[a+b][x++]));
      leds[i] = CRGB(red, green, blue);
    }
    FastLED.show();
    delay (100);

    /* Switch handling */

    while ( digitalRead(2) == 1 && digitalRead(3) == 1)
      delay(10);

    if (digitalRead(2) == 0) {
      a+=2;
      b=0;
      
      if ( a > (NUMIMGS * 2))
        a=0;
    }

    if (digitalRead(3) == 0)
      if ( images[a+1] != 0)
        b^=1;

    x=0;
    while ( digitalRead(2) != 1 || digitalRead(3) != 1) {
      delay(10);
      x++;
      
      /* Long press handling */
      if ( x == 100 ) {
        for ( i=0 ; i < NUM_LEDS ; i++) {
          leds[i] = CRGB(0, 0, 0);
        }
        FastLED.show();
        while ( digitalRead(2) != 1 || digitalRead(3) != 1)
          delay(10);
        delay(50);
        while ( digitalRead(2) == 1 && digitalRead(3) == 1)
          delay(10);
      }
    }
  }
}
